TonyMilton/Priezor/reference/aphex.png

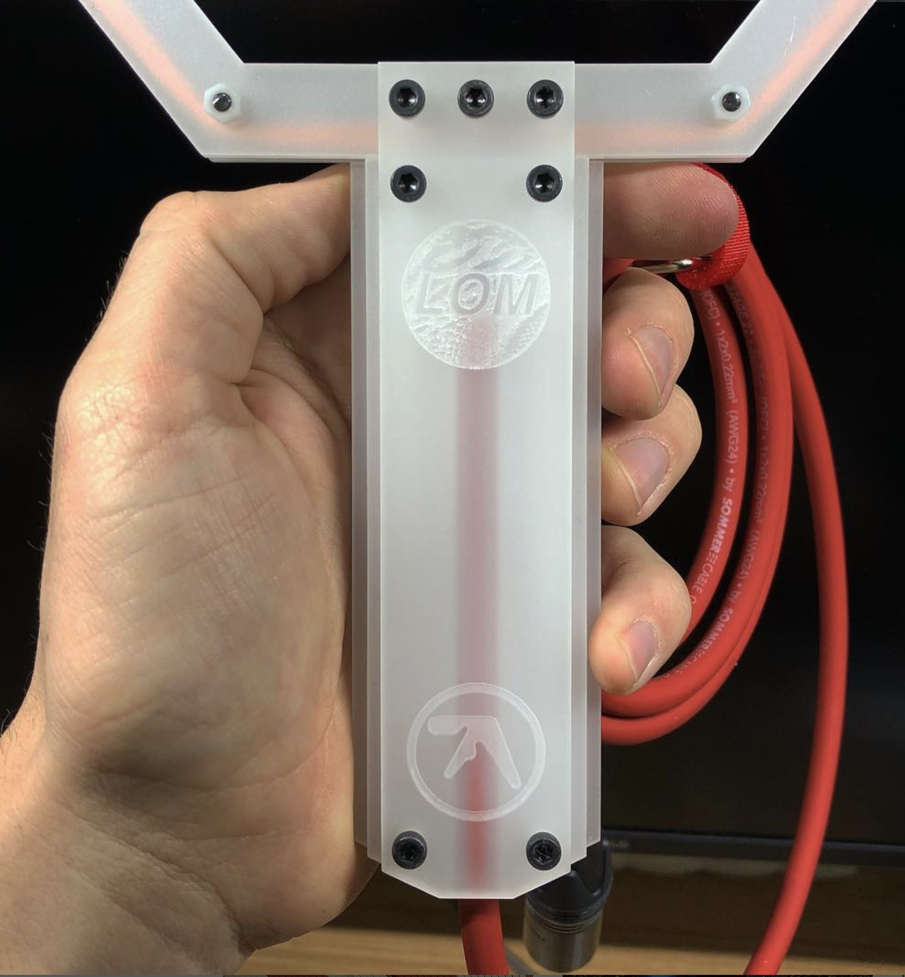
reference/aphex.png
