TonyMilton/Priezor/reference/glowy.jpg

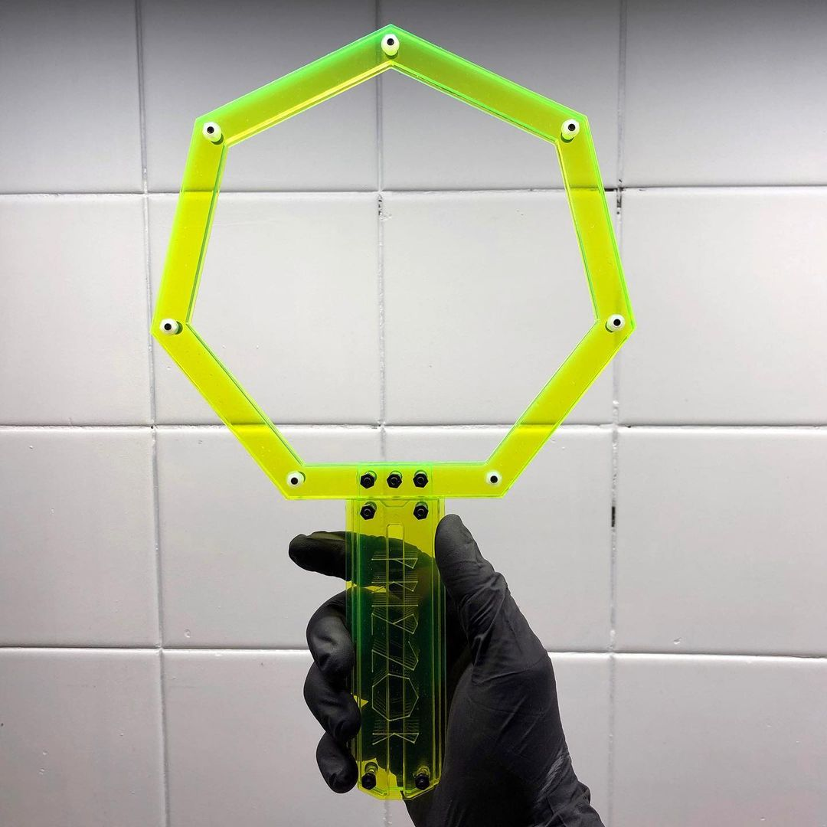
reference/glowy.jpg
